Joshua20253AU222/Proyecto-integrador-mezcla-de-unicel-/Diagramas/Conección Sistema 1.0 - 1.3.png

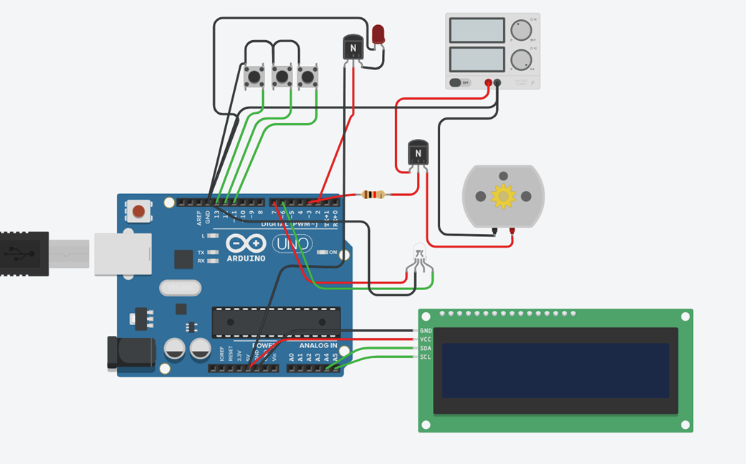
Diagramas/Conección Sistema 1.0 - 1.3.png
