Joshua20253AU222/Proyecto-integrador-mezcla-de-unicel-/Imágenes/Bomba de agua con caudalimetro .png

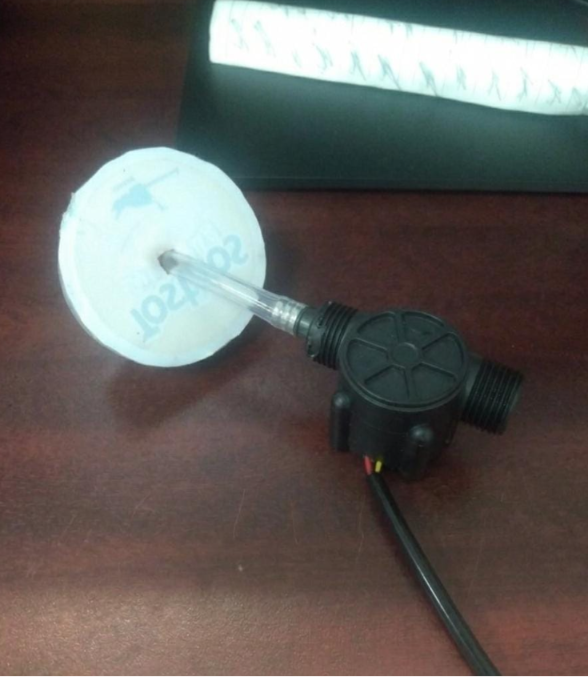
Imágenes/Bomba de agua con caudalimetro .png
