Joshua20253AU222/Proyecto-integrador-mezcla-de-unicel-/Imágenes/Brazo dosificador inclinado.png

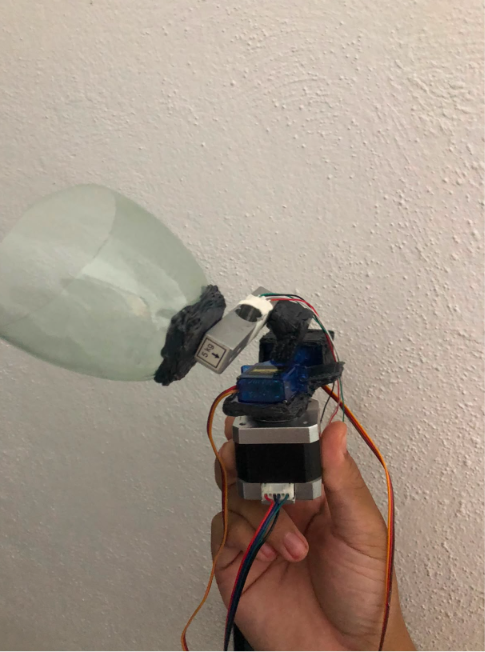
Imágenes/Brazo dosificador inclinado.png
