Joshua20253AU222/Proyecto-integrador-mezcla-de-unicel-/Imágenes/Circuito del sistema de dosificación y menú.png

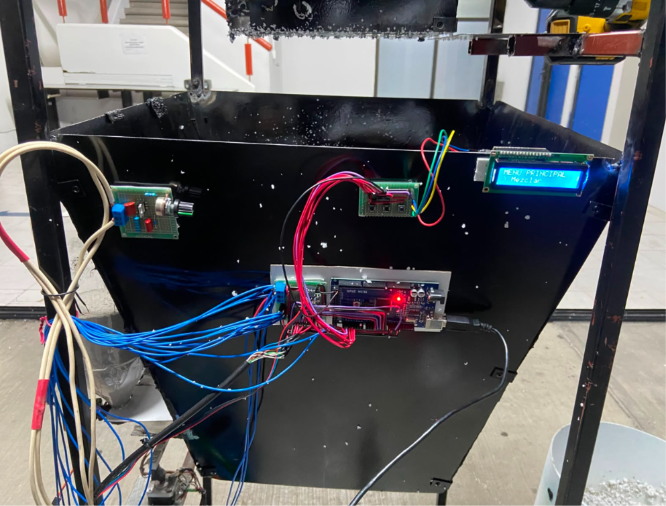
Imágenes/Circuito del sistema de dosificación y menú.png
