Joshua20253AU222/Proyecto-integrador-mezcla-de-unicel-/Imágenes/Contenedor dispensador prototipo.png

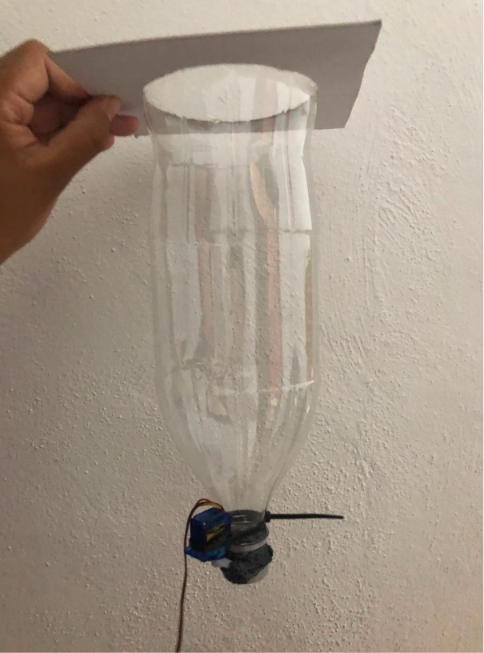
Imágenes/Contenedor dispensador prototipo.png
