Joshua20253AU222/Proyecto-integrador-mezcla-de-unicel-/Imágenes/cortes de láminas para tolva.png

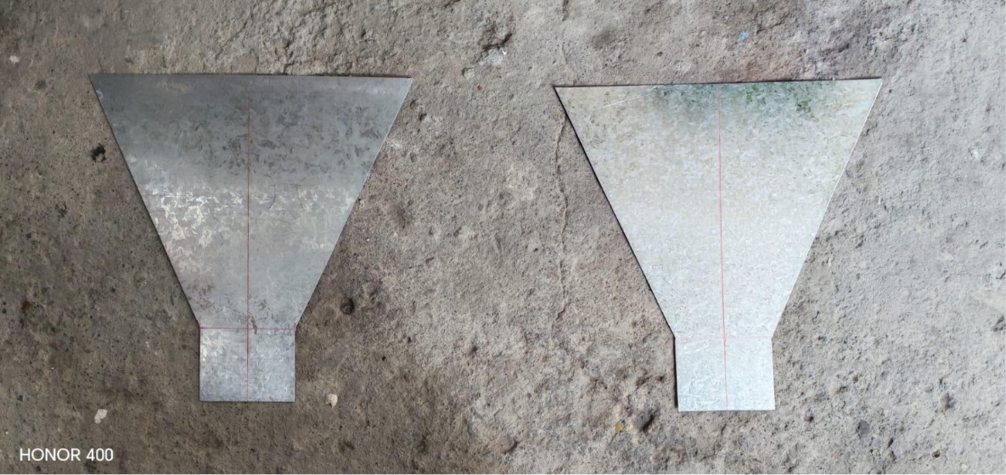
Imágenes/cortes de láminas para tolva.png
