Joshua20253AU222/Proyecto-integrador-mezcla-de-unicel-/Imágenes/Depósito de agua con bomba .png

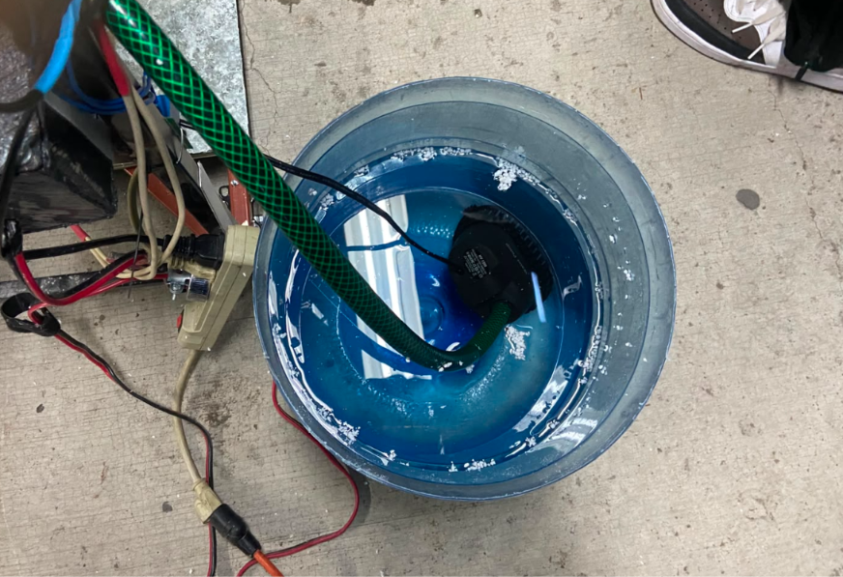
Imágenes/Depósito de agua con bomba .png
