Joshua20253AU222/Proyecto-integrador-mezcla-de-unicel-/Imágenes/Lamina.png

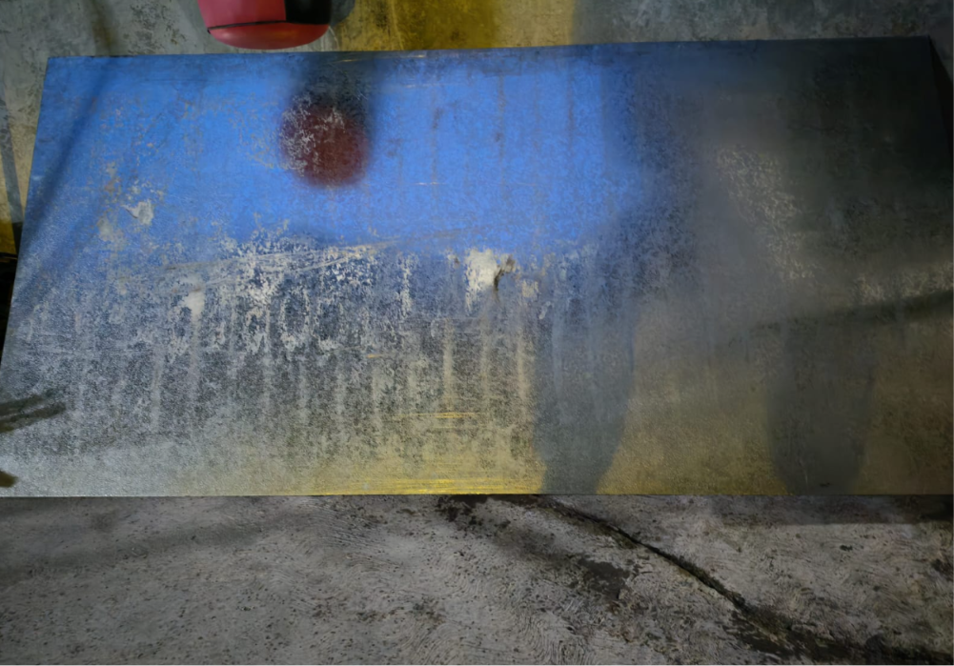
Imágenes/Lamina.png
