Joshua20253AU222/Proyecto-integrador-mezcla-de-unicel-/Imágenes/Mezcladora y riel corredizo.png

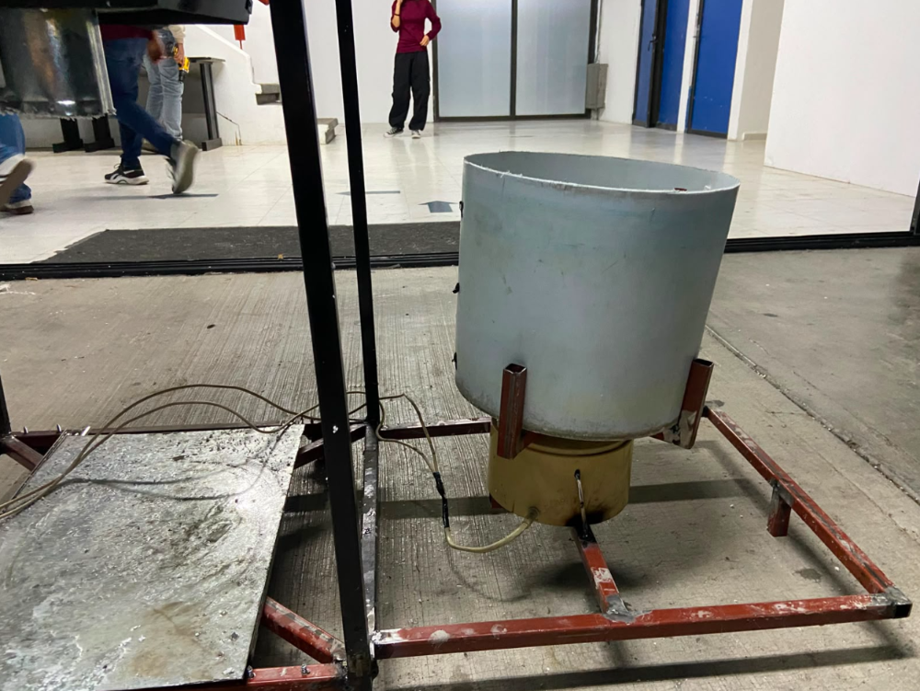
Imágenes/Mezcladora y riel corredizo.png
