Joshua20253AU222/Proyecto-integrador-mezcla-de-unicel-/Imágenes/Primeros modelos de los sistemas.png

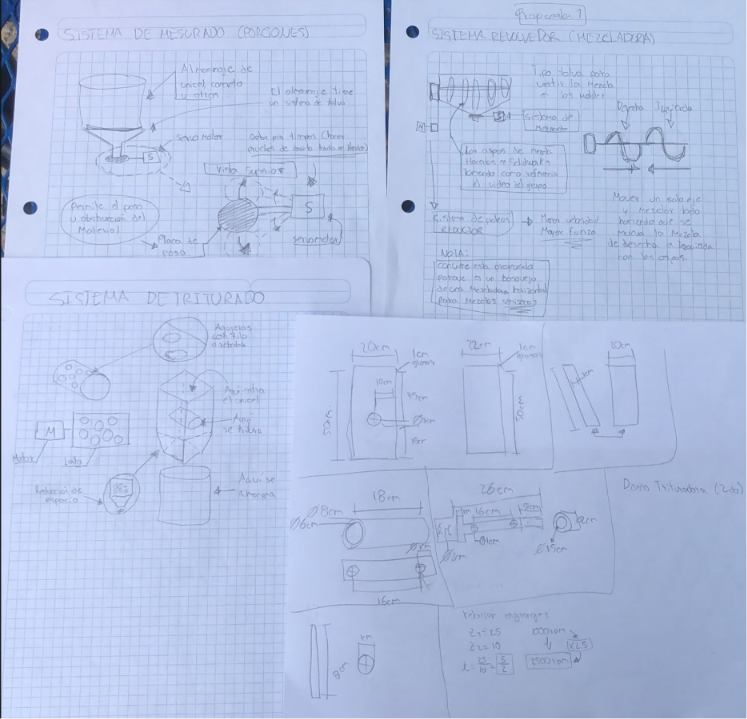
Imágenes/Primeros modelos de los sistemas.png
