Joshua20253AU222/Proyecto-integrador-mezcla-de-unicel-/Imágenes/Simulación relevador.png

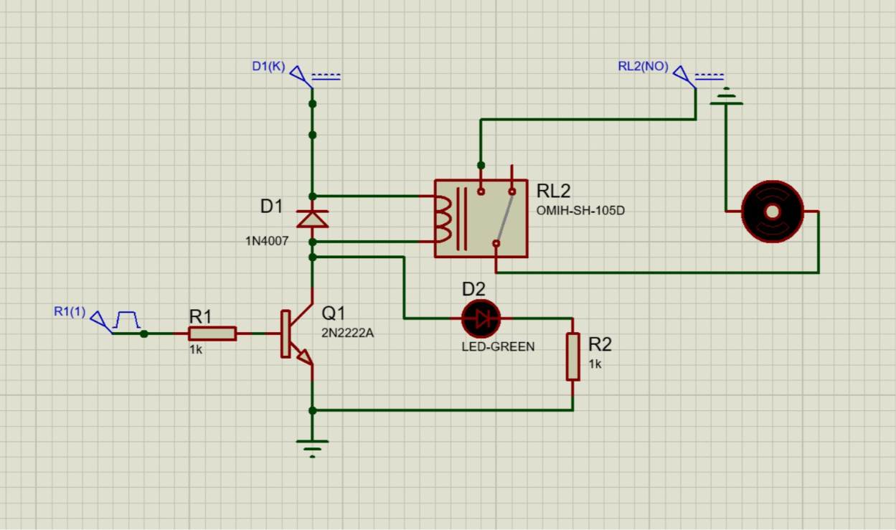
Imágenes/Simulación relevador.png
