Joshua20253AU222/Proyecto-integrador-mezcla-de-unicel-/Imágenes/Sistema de dosificación en funcionamiento.png

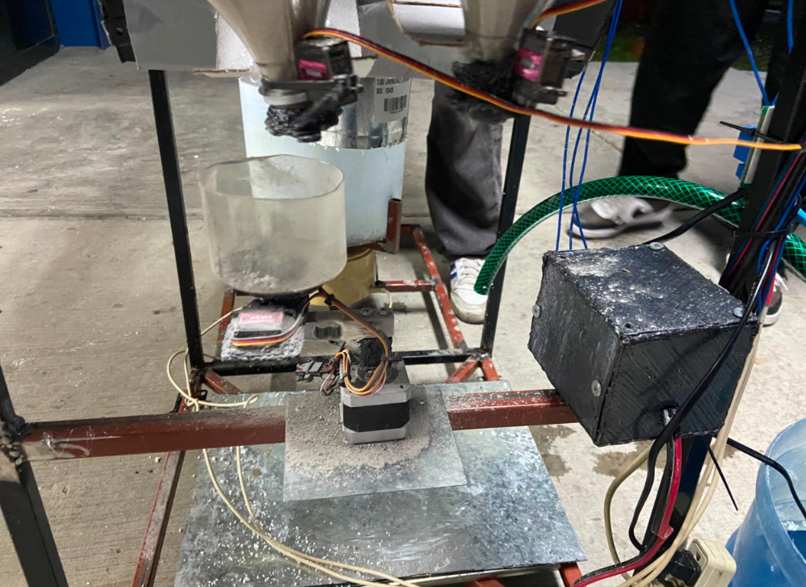
Imágenes/Sistema de dosificación en funcionamiento.png
