Joshua20253AU222/Proyecto-integrador-mezcla-de-unicel-/Imágenes/Tolva de lámina.png

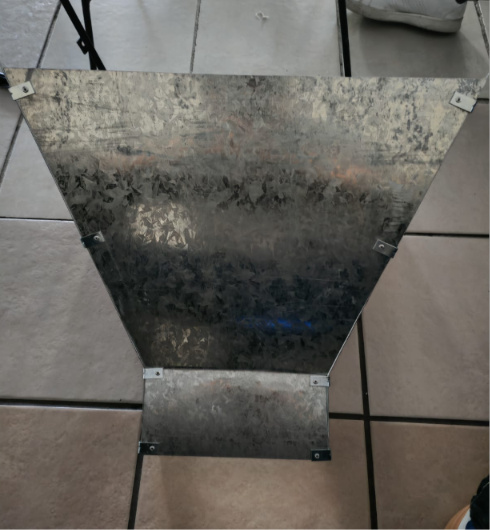
Imágenes/Tolva de lámina.png
